jimmy-vo/SenseIMU/EmbeddedHardware/v1.brd

## EAGLE design EmbeddedHardware/v1.brd (2018-03-03)

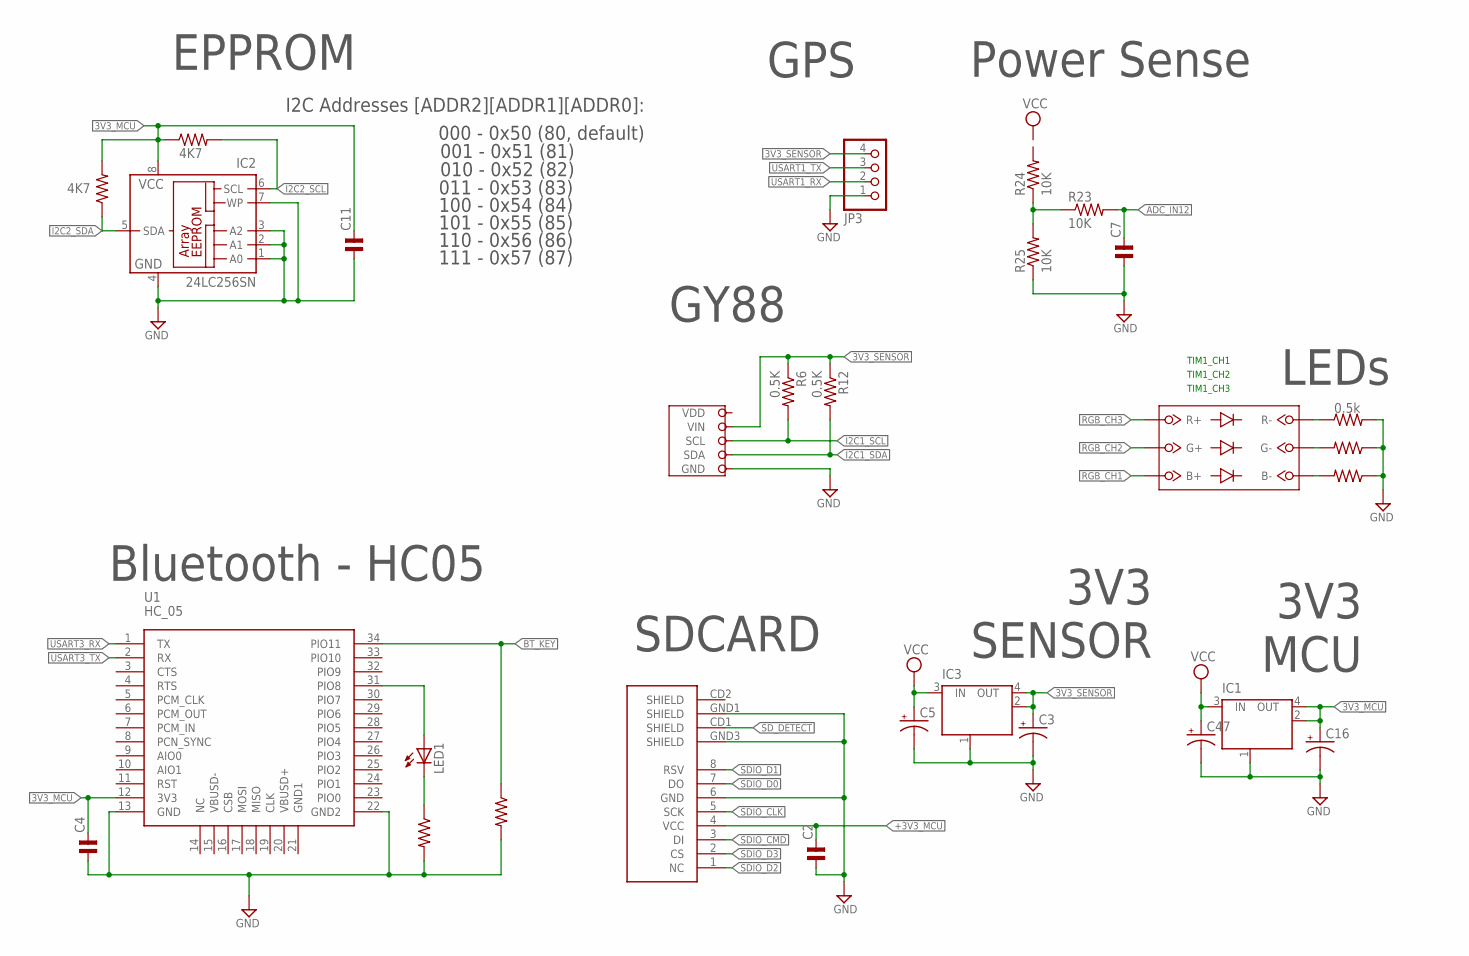
[picture p14: schematic v1.sch, part in row 1, column 1]

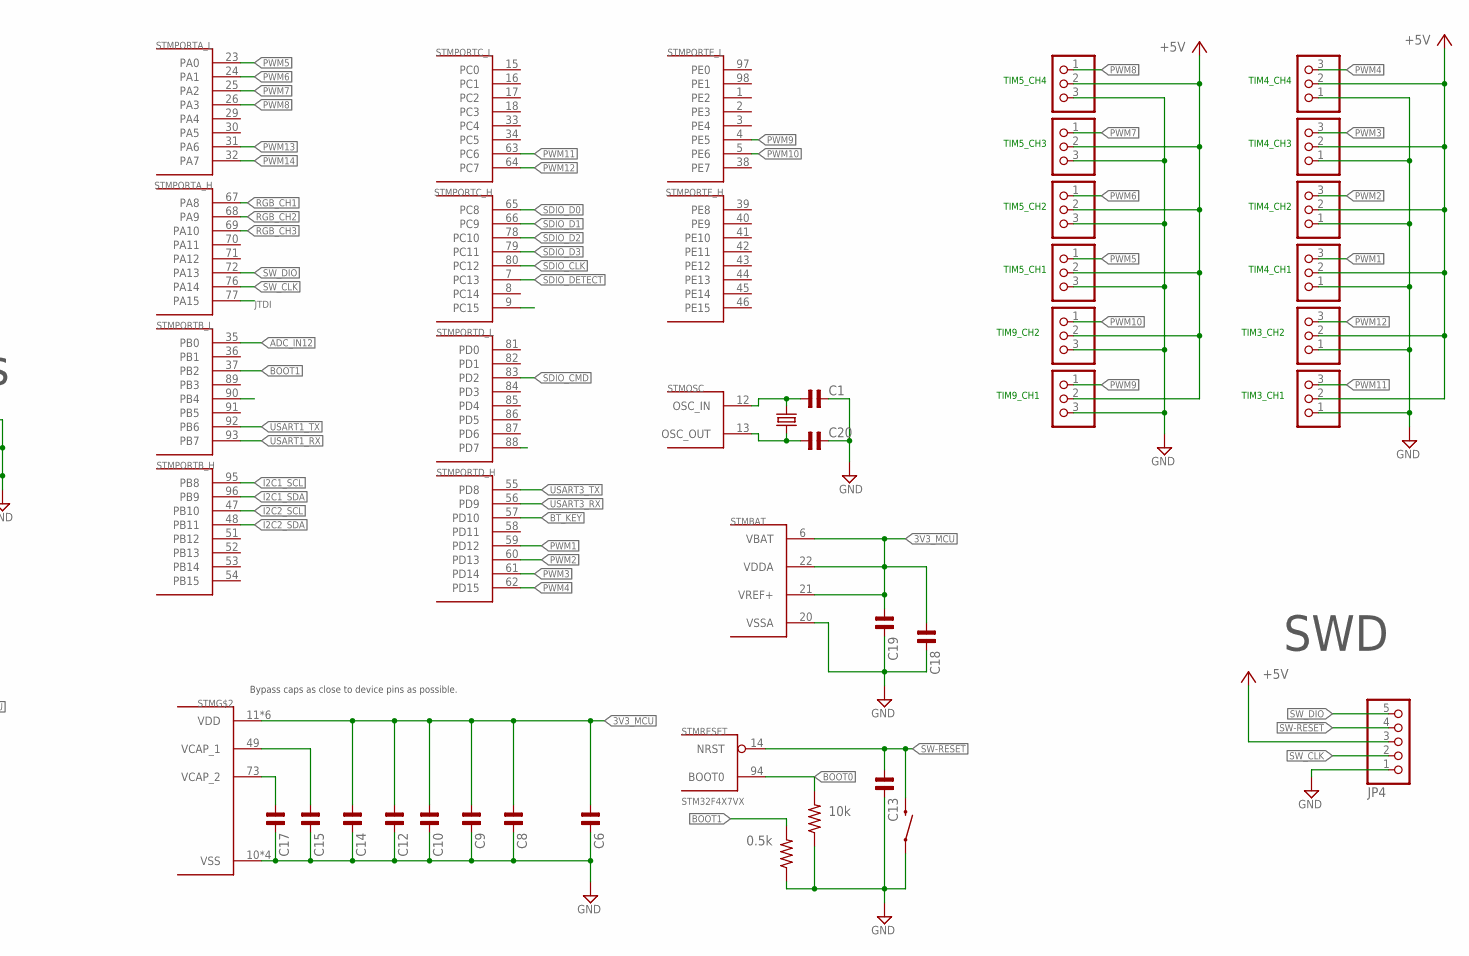
[picture p15: schematic v1.sch, part in row 1, column 2]

Parts:
C1, C2, C4, C6, C7, C8, C9, C10, C11, C12, C13, C14, C15, C17, C18, C19, C20: C-NP-SMD-0603; C-0603
C3, C5, C16, C47: CPOL-USSMCD; SMC_D
IC1, IC3: LINEAR_MC33269ST-3.3T3; LINEAR_SOT223
IC2: 24LC256SN; SO-08; DIGIKEY 24LC256-E/SN-ND
JP1, JP2, JP5, JP6, JP7, JP8, JP9, JP10, JP11, JP12, JP13, JP14: PINHD-1X3_2.54-90°; 1X03/90
JP3: PINHD-1X4; 1X04
JP4: PINHD-1X5_2.54-90°; 1X05/90
LED1: LEDCHIP-LED0805; CHIP-LED0805
R1, R2, R3, R5, R23, R24, R25, R39: 10K; SPARKFUN_0603-RES
R6, R12: 0.5K; SPARKFUN_0603-RES
R7: 10k; SPARKFUN_0603-RES
R8: 0.5k; SPARKFUN_0603-RES
R15, R16: 4K7; SPARKFUN_0603-RES
S1: RESET; TACTILE-SWITCH-1101NE; PARTNO EVQ-P7J01P
SDCARD1: microSD Socket; MICRO-SD-SOCKET-PP
STM: STM32F4X7VX; TQFP100; PARTNO STM32F427VI
U1: HC_05; BLUETOOTH_SMD
U$1: GY-88; BREAKOUT
U$6: RGB_LED; SMD
Y1: CRYSTALHC49US; HC49US

Connections:
3V3_MCU: C4.2, C6.1, C8.1, C9.1, C10.1, C11.2, C12.1, C14.1, C16.+, C18.1, C19.1, IC1.2 (OUT), IC1.4 (OUT), IC2.8 (VCC), R15.1, R16.2, STM.6 (VBAT), STM.11 (VDD), STM.19 (VDD), STM.21 (VREF+), STM.22 (VDDA), STM.28 (VDD), STM.50 (VDD), STM.75 (VDD), STM.100 (VDD), U1.12 (3V3)
3V3_SENSOR: C3.+, IC3.2 (OUT), IC3.4 (OUT), JP3.4, R6.1, R12.1, U$1.2 (VIN)
+3V3_MCU: C2.2, SDCARD1.4 (VCC)
+5V: JP1.2, JP2.2, JP4.3, JP5.2, JP6.2, JP7.2, JP8.2, JP9.2, JP10.2, JP11.2, JP12.2, JP13.2, JP14.2
ADC_IN12: C7.2, R23.2, STM.35 (PB0)
BOOT0: R7.2, STM.94 (BOOT0)
BOOT1: R8.2, STM.37 (PB2)
BT_KEY: R5.1, STM.57 (PD10), U1.34 (PIO11)
GND: C1.2, C2.1, C3.-, C4.1, C5.-, C6.2, C7.1, C8.2, C9.2, C10.2, C11.1, C12.2, C13.2, C14.2, C15.2, C16.-, C17.2, C18.2, C19.2, C20.2, C47.-, IC1.1 (GND/ADJ), IC2.1 (A0), IC2.2 (A1), IC2.3 (A2), IC2.4 (GND), IC2.7 (WP), IC3.1 (GND/ADJ), JP1.3, JP2.3, JP3.1, JP4.1, JP5.3, JP6.3, JP7.1, JP8.3, JP9.1, JP10.1, JP11.3, JP12.1, JP13.1, JP14.1, R1.2, R2.1, R3.2, R5.2, R7.1, R8.1, R25.1, R39.1, S1.P$1 (1), SDCARD1.6 (GND), SDCARD1.GND1 (SHIELD), SDCARD1.GND3 (SHIELD), STM.10 (VSS), STM.20 (VSSA), STM.27 (VSS), STM.74 (VSS), STM.99 (VSS), U1.13 (GND), U1.22 (GND2), U$1.3 (GND)
I2C1_SCL: R6.2, STM.95 (PB8), U$1.4 (SCL)
I2C1_SDA: R12.2, STM.96 (PB9), U$1.5 (SDA)
I2C2_SCL: IC2.6 (SCL), R15.2, STM.47 (PB10)
I2C2_SDA: IC2.5 (SDA), R16.1, STM.48 (PB11)
JTDI: STM.77 (PA15)
unnamed: C1.1, STM.12 (OSC_IN), Y1.2
unnamed: R39.2, U$6.G-
unnamed: R2.2, U$6.B-
unnamed: R3.1, U$6.R-
unnamed: LED1.A, U1.31 (PIO8)
unnamed: LED1.C, R1.1
unnamed: R23.1, R24.1, R25.2
unnamed: C20.1, STM.13 (OSC_OUT), Y1.1
unnamed: C17.1, STM.73 (VCAP_2)
unnamed: C15.1, STM.49 (VCAP_1)
PWM1: JP7.3, STM.59 (PD12)
PWM2: JP9.3, STM.60 (PD13)
PWM3: JP10.3, STM.61 (PD14)
PWM4: JP12.3, STM.62 (PD15)
PWM5: JP1.1, STM.23 (PA0)
PWM6: JP5.1, STM.24 (PA1)
PWM7: JP11.1, STM.25 (PA2)
PWM8: JP6.1, STM.26 (PA3)
PWM9: JP2.1, STM.4 (PE5)
PWM10: JP8.1, STM.5 (PE6)
PWM11: JP13.3, STM.63 (PC6)
PWM12: JP14.3, STM.64 (PC7)
PWM13: STM.31 (PA6)
PWM14: STM.32 (PA7)
RGB_CH1: STM.67 (PA8), U$6.B+
RGB_CH2: STM.68 (PA9), U$6.G+
RGB_CH3: STM.69 (PA10), U$6.R+
SDIO_CLK: SDCARD1.5 (SCK), STM.80 (PC12)
SDIO_CMD: SDCARD1.3 (DI), STM.83 (PD2)
SDIO_D0: SDCARD1.7 (DO), STM.65 (PC8)
SDIO_D1: SDCARD1.8 (RSV), STM.66 (PC9)
SDIO_D2: SDCARD1.1 (NC), STM.78 (PC10)
SDIO_D3: SDCARD1.2 (CS), STM.79 (PC11)
SDIO_DETECT: STM.7 (PC13)
SD_DETECT: SDCARD1.CD1 (SHIELD)
SW-!RESET: C13.1, JP4.4, S1.P$2 (2), STM.14 (NRST)
SW_CLK: JP4.2, STM.76 (PA14)
SW_DIO: JP4.5, STM.72 (PA13)
USART1_RX: JP3.2, STM.93 (PB7)
USART1_TX: JP3.3, STM.92 (PB6)
USART3_RX: STM.56 (PD9), U1.1 (TX)
USART3_TX: STM.55 (PD8), U1.2 (RX)
VCC: C5.+, C47.+, IC1.3 (IN), IC3.3 (IN)

Notes on the sheet:
Bypass caps as close to device pins as possible.
SWD
LEDs
GPS
GY88
TIM5_CH1
TIM5_CH2
TIM1_CH1
TIM1_CH2
TIM1_CH3
TIM4_CH1
TIM4_CH2
I2C Addresses [ADDR2][ADDR1][ADDR0]:
000 - 0x50 (80, default)
001 - 0x51 (81)
010 - 0x52 (82)
011 - 0x53 (83)
100 - 0x54 (84)
101 - 0x55 (85)
110 - 0x56 (86)
111 - 0x57 (87)
EPPROM
TIM5_CH3
TIM5_CH4
3V3 MCU
Bluetooth - HC05
SDCARD
Power Sense
3V3 SENSOR
TIM4_CH4
TIM4_CH3
TIM9_CH2
TIM9_CH1
TIM3_CH1
TIM3_CH2

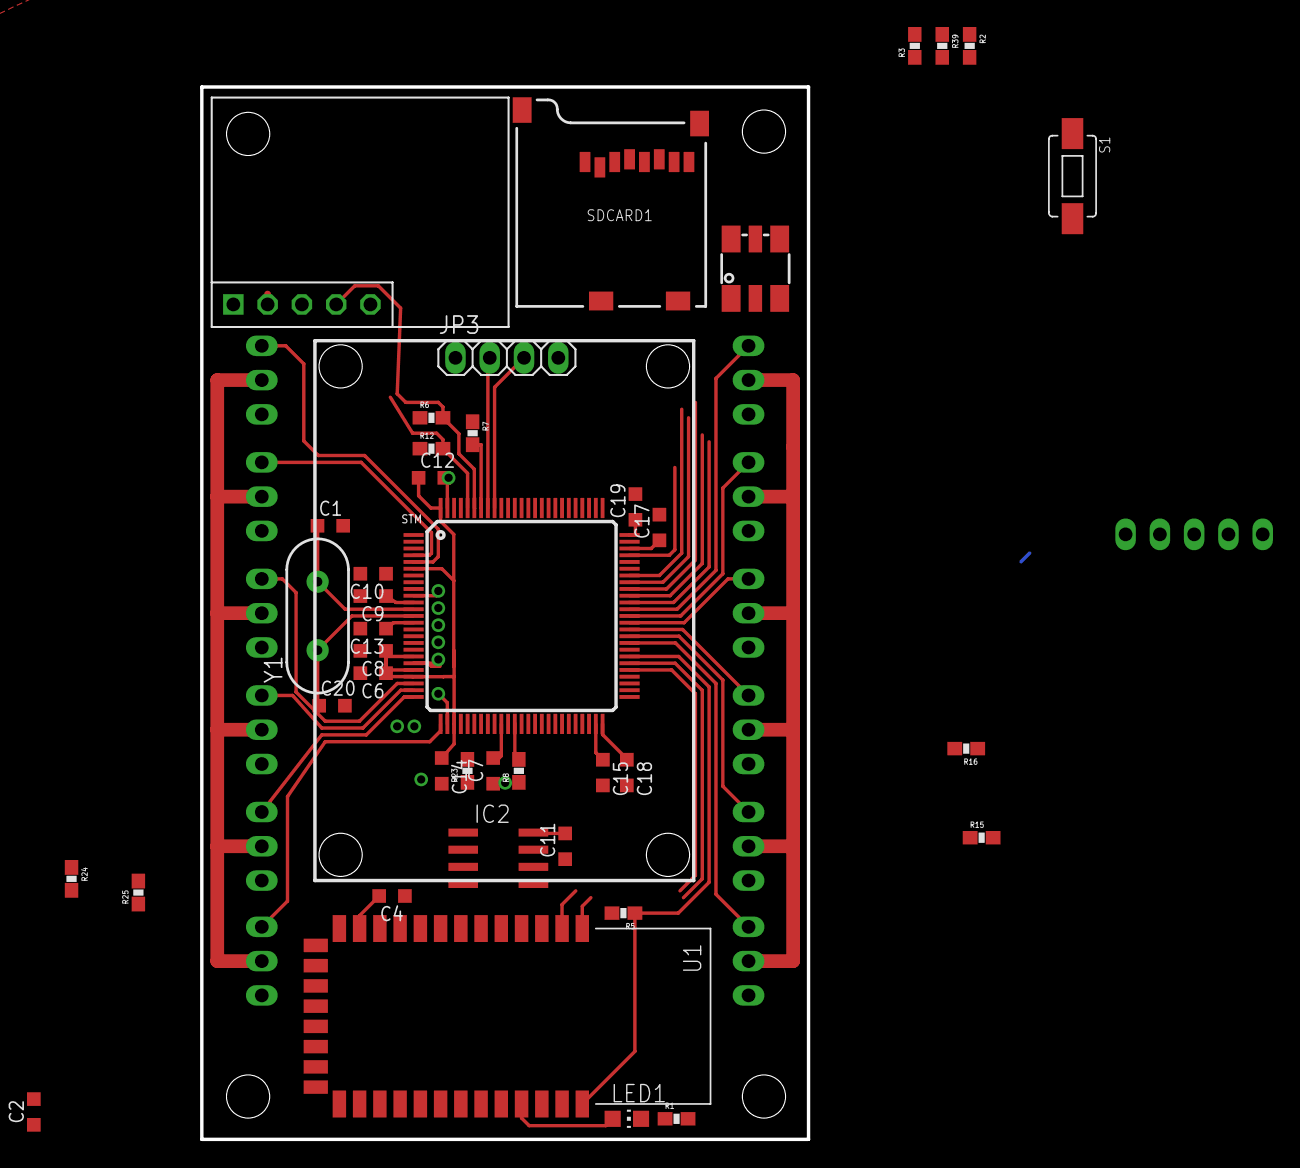
[picture p16: board v1.brd from above]

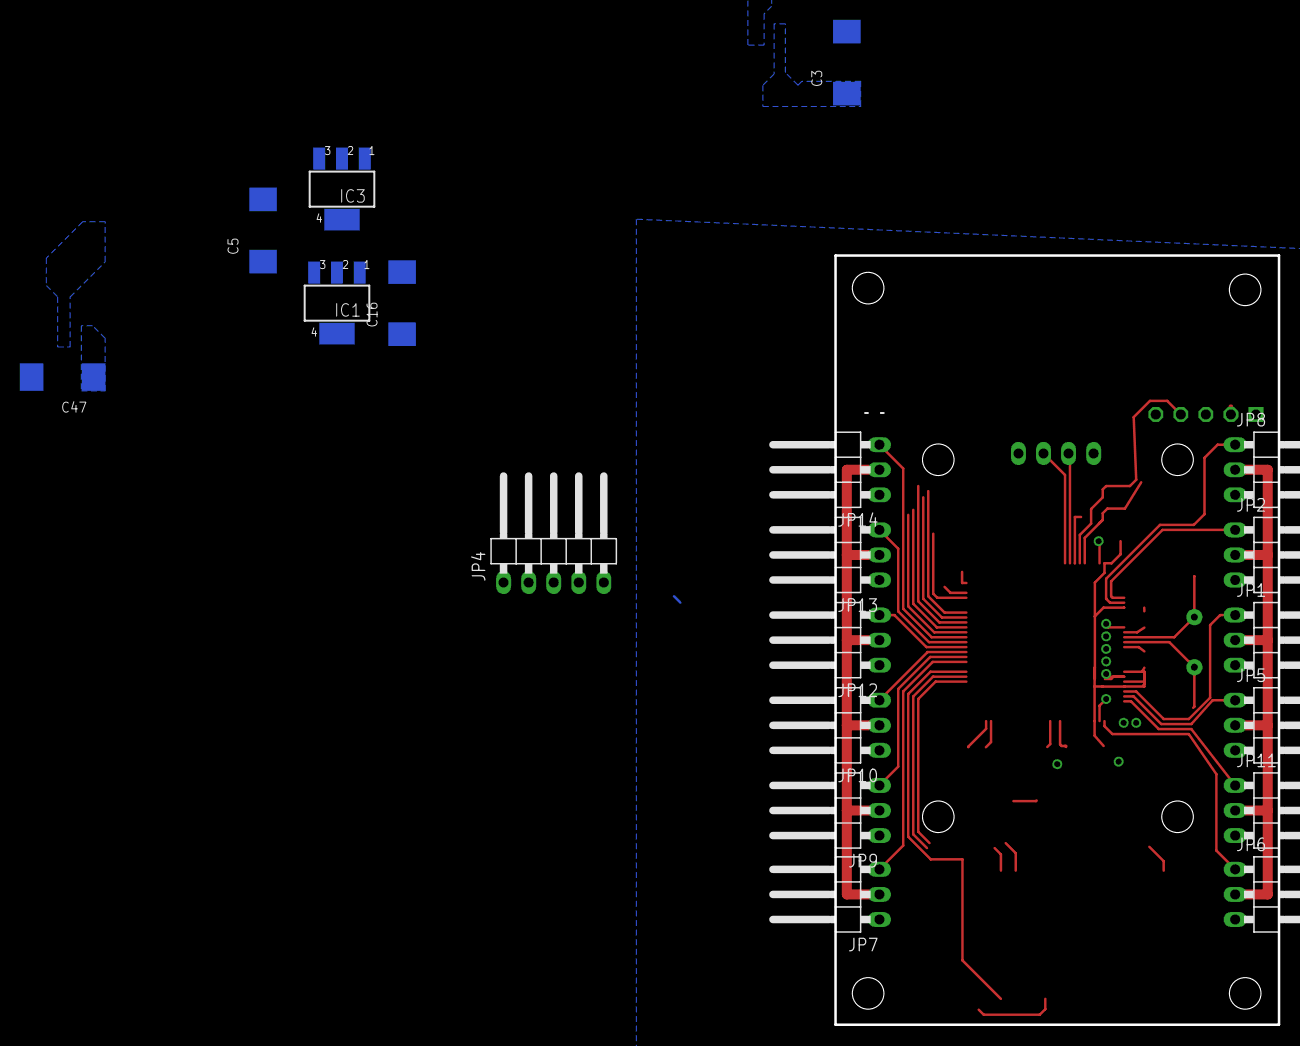
[picture p17: board v1.brd from below]

Board: 2 copper layers, 45.0 x 78.0 mm, 60 parts (19 on the bottom side), 52 nets.
