jimmy-vo/SenseIMU/EmbeddedSoftware/_Code_/Commnunication/Serial_Link_string.h

#include "BoardConfig.h"


extern char *String_FATFS_Status[];
extern char *String_I2C_Status[];
extern char *String_HMC5883_Status[];
extern char *String_MPU6050_Status[];
extern char *String_EPPROM_Status[];
extern char *String_PARAMETER_Status[];
extern char *String_PARAMETER_Type[];
extern char *String_CALIB_Status[];
extern char *String_Algorithm[];
extern char *String_SENSOR_Status[];
extern char *String_ALGORITHM_Status[];
