jimmy-vo/SenseIMU/EmbeddedSoftware/_Code_/INCLUDE.h

#include "Dev_USART.h"
#include "Dev_I2C.h"
#include "Dev_TIMER.h"

#include "Timing_Manage.h"
#include "RGB.h"
#include "Button.h"
#include "Voltage_FB.h"

#include "SENSOR_DATA.h"

#include "Serial_Link.h"
#include "EEPROM.h"
#include "SDCARD.h"
#include "Parameter.h"

#include "Algorithm.h"
#include "Calibration.h"
